Lixxxymaster/Coursework/LTS_simulation/BELL.asc

C1: cap; 0.01µ
C2: cap; 47µ
C3: cap; 0.1µ
R1: res; 2.2k
R2: res; 39k
R3: res; 100k
R4: res; 2.2k
R5: res; 23.5k
U1: 555_
U2: 555_
Vin: voltage-; 9
Named nets: 0, 1_U1, 8_U1, 7_U1, 6_U1, 5_U1, 4_U1, 3_U1, 2_U1, 5_U2, 6_U2, 7_U2, 1_U2, 2_U2, 3_U2, 4_U2, 8_U2
.tran 5
